qoq/uknc_sd_fdd/KiCad/uknc_fdd_sds.sch

## KiCad design KiCad/uknc_fdd_sds.sch (2021-02-01)

Schematic: uknc_fdd_sds.sch

Parts:
C1: 1uF; C_Disc_D7.0mm_W2.5mm_P5.00mm
C2, C3, C4, C5: 0.1; C_Disc_D7.0mm_W2.5mm_P5.00mm
C6: 10uf; CP_Radial_D6.3mm_P2.50mm
D2, D3, D4: 1N4148; D_DO-35_SOD27_P7.62mm_Horizontal
LED1: LED; LED_D5.0mm
R1: 10K; R_Axial_DIN0207_L6.3mm_D2.5mm_P7.62mm_Horizontal
R2, R3, R4, R5: 1K; R_Axial_DIN0207_L6.3mm_D2.5mm_P7.62mm_Horizontal
U1: CY8C4245AXI; TQFP-44_10x10mm_P0.8mm
U2: L78L33; TO-92L_HandSolder
X1: SNP15-48; SNP15-48-BOARD
X2: SD CARD; PJS008-2120-0_minisd
X3: SWD; PinHeader_1x05_P2.54mm_Vertical
ZD1: 3v3; D_DO-35_SOD27_P7.62mm_Horizontal
