qoq/uknc_sd_fdd/PSoC/ROM_CART.cydsn/romctr_basic.h

/* Created by bin2c (c)Jarik */
const char data_basic[]={ 
160,0,194,21,68,0,50,144,3,0,193,21,
5,0,195,21,78,0,2,1,223,148,190,253,
223,139,188,253,253,128,70,126,202,139,238,2,
3,10,193,21,110,11,194,21,171,47,67,100,
67,11,131,126,131,10,228,2,95,0,110,11,
0,0,0,0,66,0,2,0,0,8,17,0,
128,0,110,11,171,47,68,0,255,255,0,0,
0,0,0,0,0,0,255,255,0,0,255,255,
0,0,255,255,0,0,255,255,0,0,255,255,
0,0,255,255,0,0,255,255,0,0,255,255,
0,0,255,255,0,0,255,255,198,21,0,2,
192,21,134,2,1,10,194,21,6,0,80,20,
130,126,208,23,48,0,208,23,50,0,208,23,
164,0,208,23,166,0,31,10,158,2,223,21,
60,112,160,253,208,23,162,253,223,21,198,32,
162,253,159,10,160,253,208,23,162,253,223,21,
128,1,162,253,55,10,194,246,223,21,0,224,
28,2,223,23,28,2,26,2,55,10,102,246,
55,10,152,246,247,21,200,0,54,246,192,21,
48,2,208,21,10,0,208,21,10,0,16,10,
1,16,208,21,65,64,208,21,62,46,80,20,
80,20,193,21,10,0,208,21,84,71,67,126,
31,10,88,2,247,9,122,12,31,10,52,2,
247,9,224,3,119,0,14,1,198,21,0,2,
183,8,66,6,247,9,98,12,192,21,12,0,
247,9,140,13,243,1,247,11,220,245,44,129,
198,21,0,2,192,21,10,0,247,9,120,13,
119,0,144,1,70,137,247,9,250,3,192,21,
12,0,247,9,102,13,247,9,132,21,247,9,
176,68,192,21,134,2,1,10,194,21,6,0,
17,20,130,126,31,20,48,0,31,20,50,0,
31,20,164,0,31,20,166,0,223,21,60,112,
160,253,31,20,162,253,159,10,160,253,31,20,
162,253,0,0,198,21,0,2,31,10,84,2,
247,29,234,245,234,245,247,157,233,245,230,245,
247,11,238,245,8,3,193,21,13,0,0,10,
247,9,22,18,67,126,247,9,148,68,247,9,
80,68,193,21,87,14,194,21,5,0,247,9,
36,13,247,11,68,245,33,4,247,11,148,245,
4,3,196,29,142,245,55,10,138,245,55,33,
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
long int data_length=24576;
