qoq/uknc_sd_fdd/PSoC/mpi_rom_emu.cydsn/sd/integer.h

/*-------------------------------------------*/
/* Integer type definitions for FatFs module */
/*-------------------------------------------*/
#include <stdint.h>

#ifndef _INTEGER
#define _INTEGER

typedef int32_t INT_;
typedef uint32_t	UINT;
typedef int8_t CHAR_;
typedef uint8_t	UCHAR;
typedef uint8_t	BYTE;
typedef int16_t	SHORT;
typedef uint16_t USHORT;
typedef uint16_t WORD;
typedef uint16_t WCHAR;
typedef int32_t	LONG_;
typedef uint32_t ULONG;
typedef uint32_t DWORD;
typedef DWORD LBA_t;

#endif
